Non-Sense/EhHHKB2/firmware/scripts/out/01_status_bt_named.png

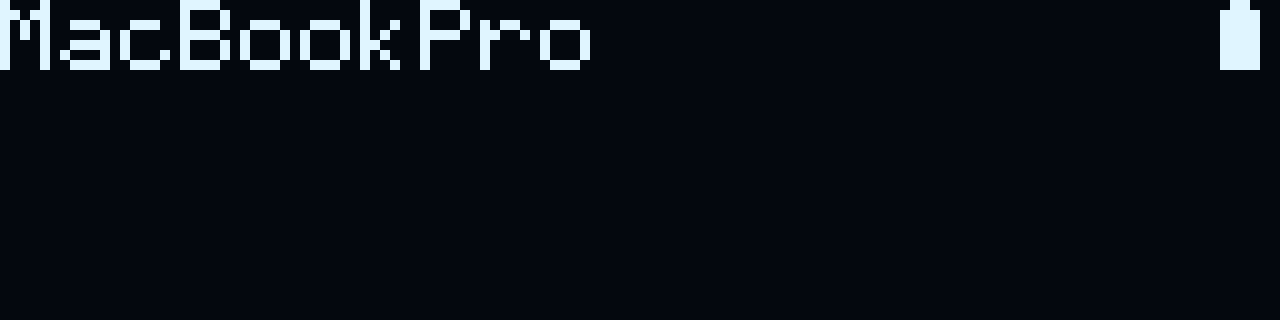
firmware/scripts/out/01_status_bt_named.png
