Non-Sense/EhHHKB2/firmware/scripts/out/10_menu_top.png

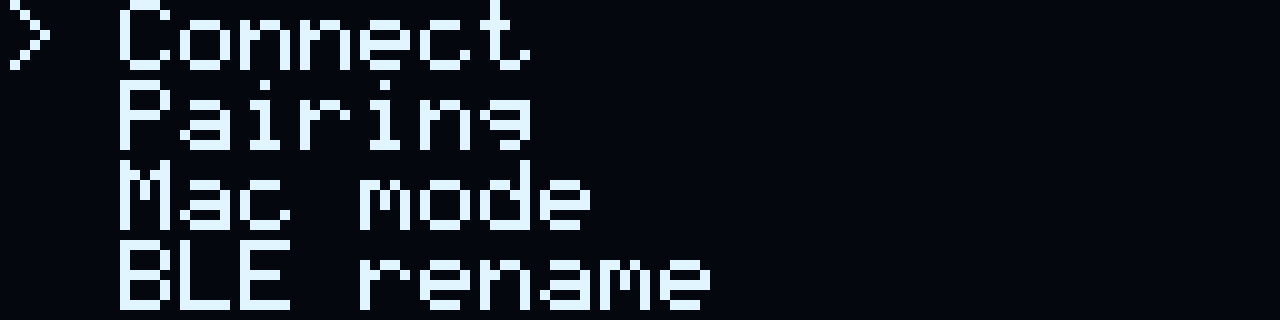
firmware/scripts/out/10_menu_top.png
