Non-Sense/EhHHKB2/firmware/scripts/out/12_menu_connect.png

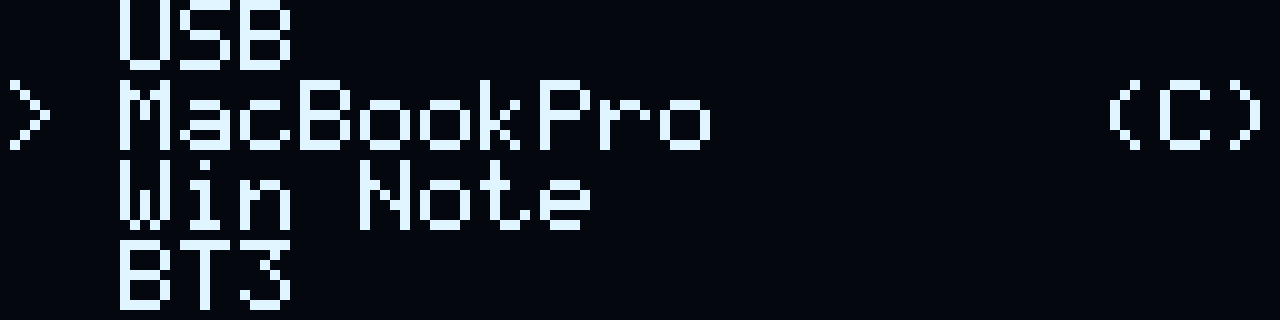
firmware/scripts/out/12_menu_connect.png
