Non-Sense/EhHHKB2/firmware/scripts/out/14_menu_rename.png

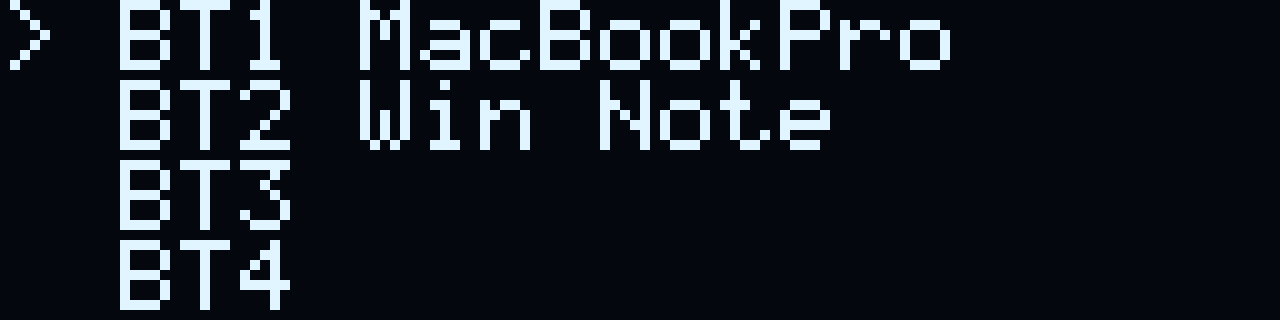
firmware/scripts/out/14_menu_rename.png
