Non-Sense/EhHHKB2/firmware/scripts/out/19_menu_misc.png

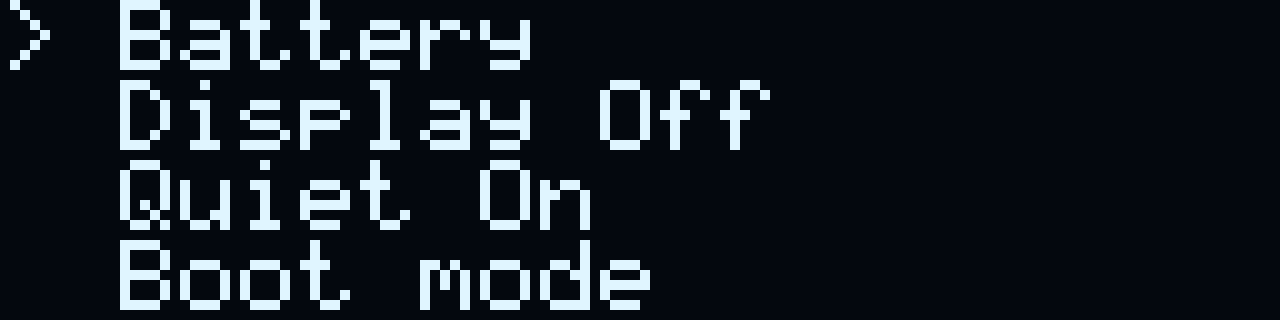
firmware/scripts/out/19_menu_misc.png
