Non-Sense/EhHHKB2/firmware/scripts/out/20_menu_battery.png

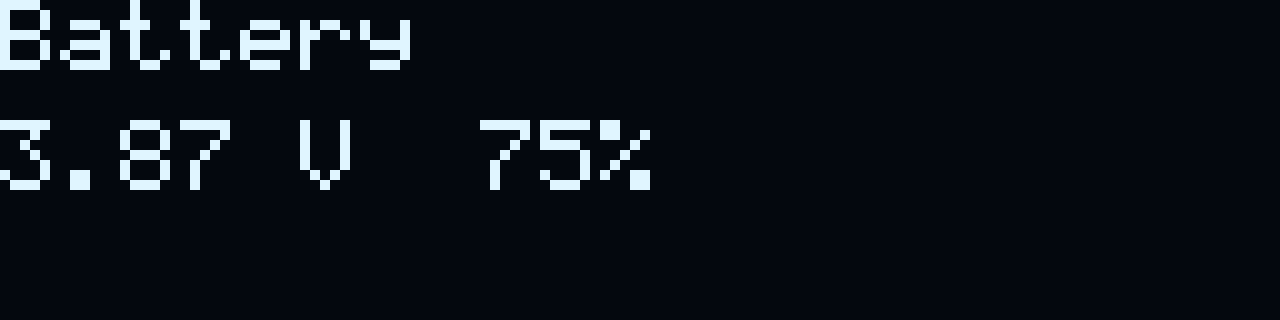
firmware/scripts/out/20_menu_battery.png
