Non-Sense/EhHHKB2/firmware/scripts/out/21_menu_boot.png

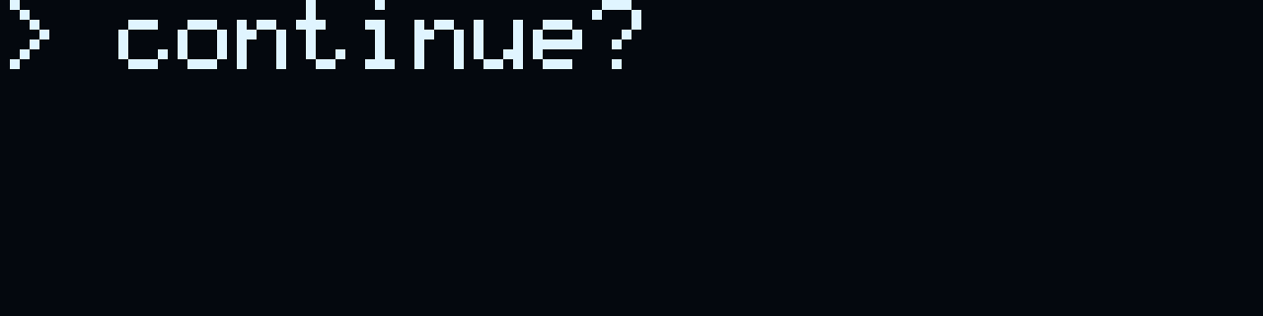
firmware/scripts/out/21_menu_boot.png
