Non-Sense/EhHHKB2/firmware/scripts/out/font_sheet.png

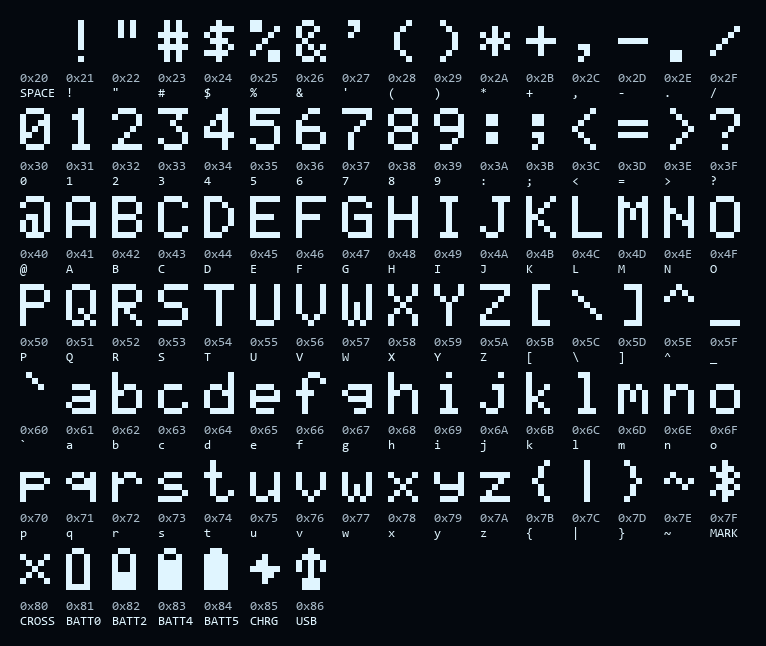
firmware/scripts/out/font_sheet.png
